JonasKaad/ProgrammingOfRobots/models/3DPrints/attachments/6_axle.stl

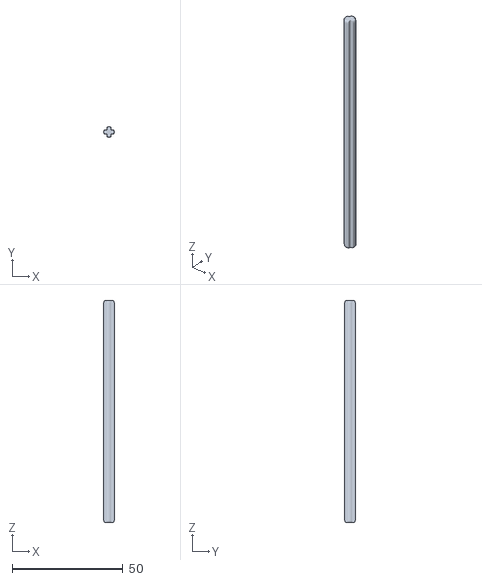
[picture p33: CAD file, 2024-05-22]
models/3DPrints/attachments/6_axle.stl
4.75 x 4.75 x 100.2
