JonasKaad/ProgrammingOfRobots/models/3DPrints/garage_bar/LBar_long.stl

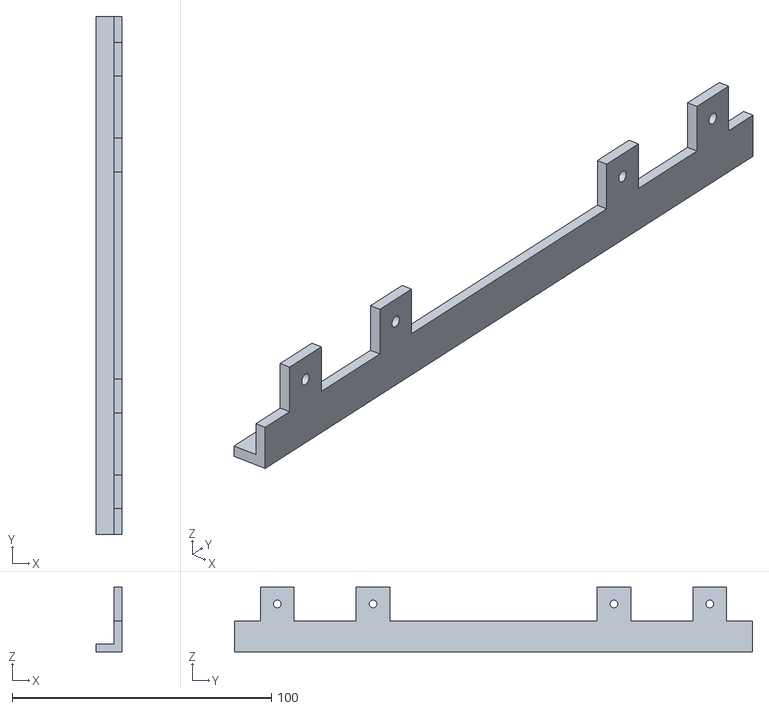
[picture p34: CAD file, 2024-05-22]
models/3DPrints/garage_bar/LBar_long.stl
10.0 x 200.0 x 25.0
