JonasKaad/ProgrammingOfRobots/models/3DPrints/gears/wormdrive_gear.stl

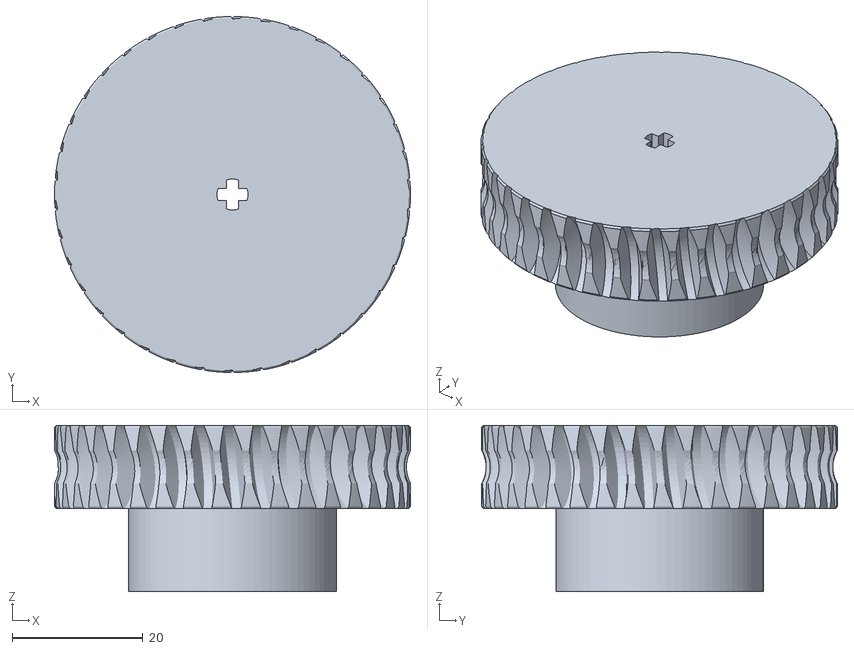
[picture p35: CAD file, 2024-05-22]
models/3DPrints/gears/wormdrive_gear.stl
54.4 x 54.4 x 25.4
