JonasKaad/ProgrammingOfRobots/models/3DPrints/supports/left_worm_drive_support.stl

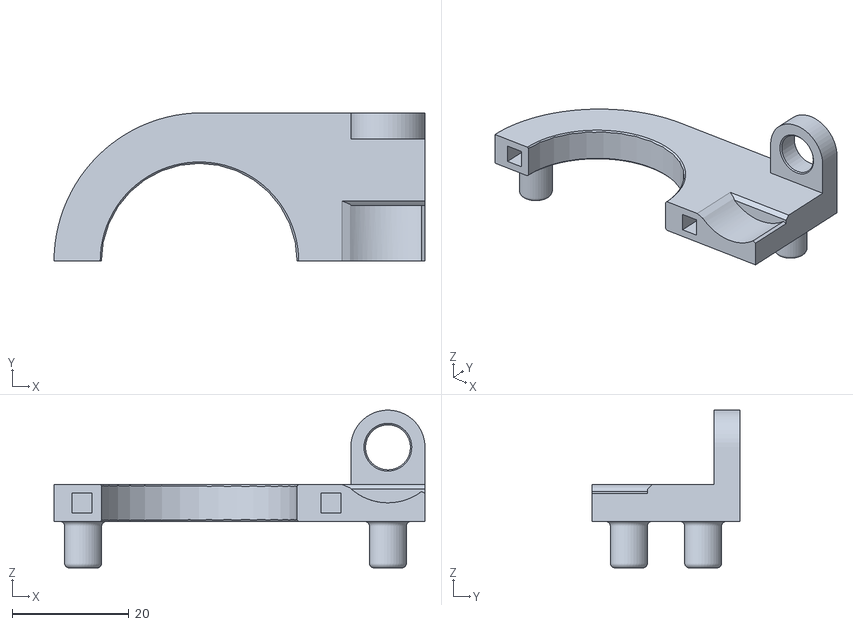
[picture p36: CAD file, 2024-05-22]
models/3DPrints/supports/left_worm_drive_support.stl
63.5 x 25.4 x 27.0
