JonasKaad/ProgrammingOfRobots/Unity/GarageTwin/Assets/Gears/WormDrive/worm_bar_gear.obj

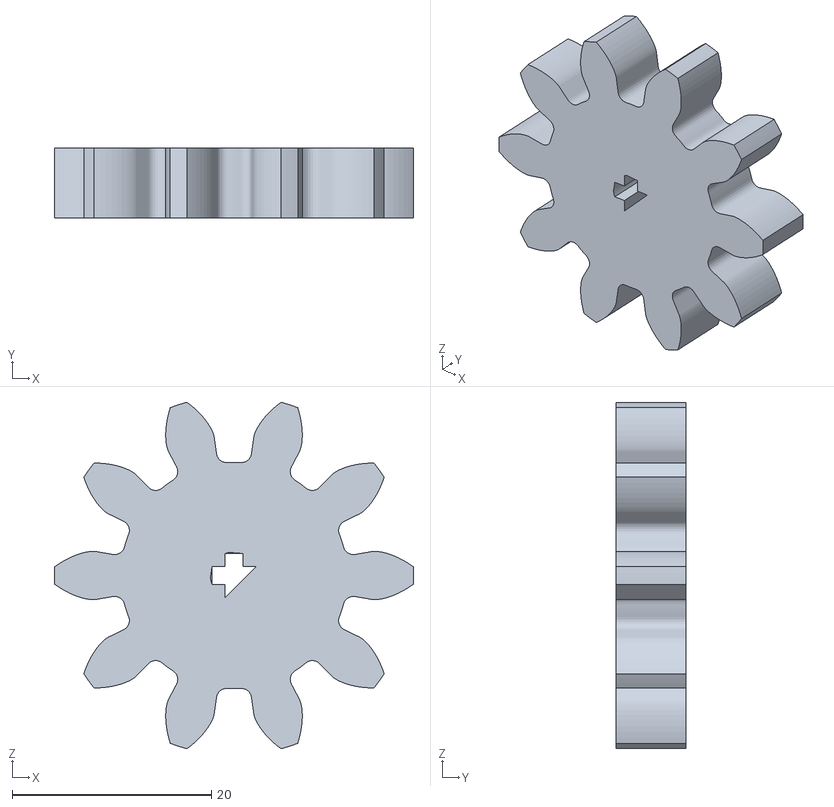
[picture p37: CAD file, 2024-05-13]
Unity/GarageTwin/Assets/Gears/WormDrive/worm_bar_gear.obj
36.0 x 7.00 x 34.7
