JonasKaad/ProgrammingOfRobots/models/3DPrints/attachments/door_connection_to_pinion.stl

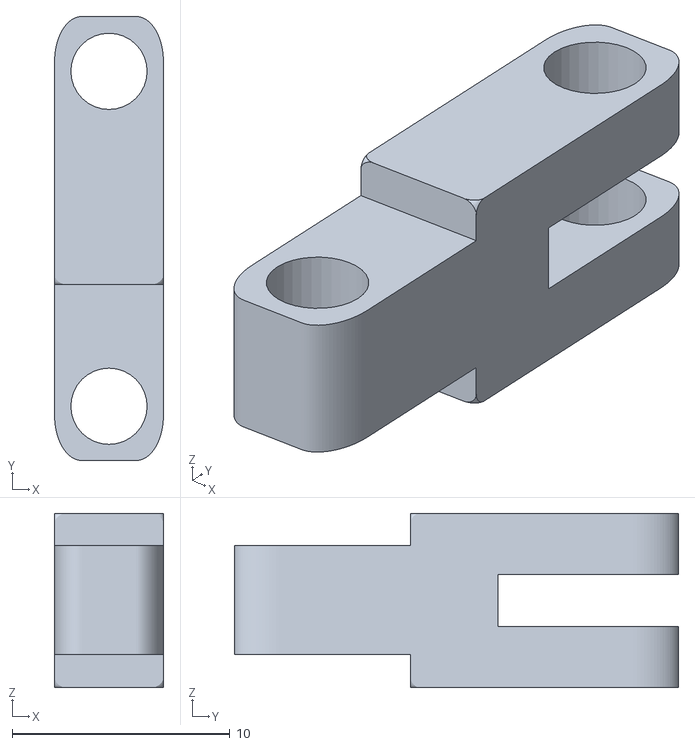
[picture p38: CAD file, 2024-05-22]
models/3DPrints/attachments/door_connection_to_pinion.stl
5.00 x 20.4 x 8.00
