JonasKaad/ProgrammingOfRobots/models/3DPrints/gears/pinion_gear.stl

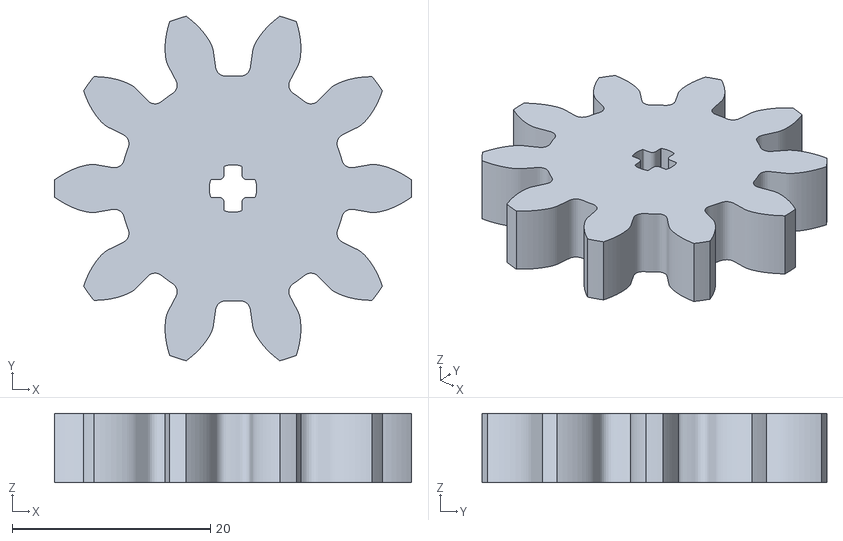
[picture p39: CAD file, 2024-05-22]
models/3DPrints/gears/pinion_gear.stl
36.0 x 34.7 x 7.00
