JonasKaad/ProgrammingOfRobots/models/3DPrints/supports/right_worm_drive_support.stl

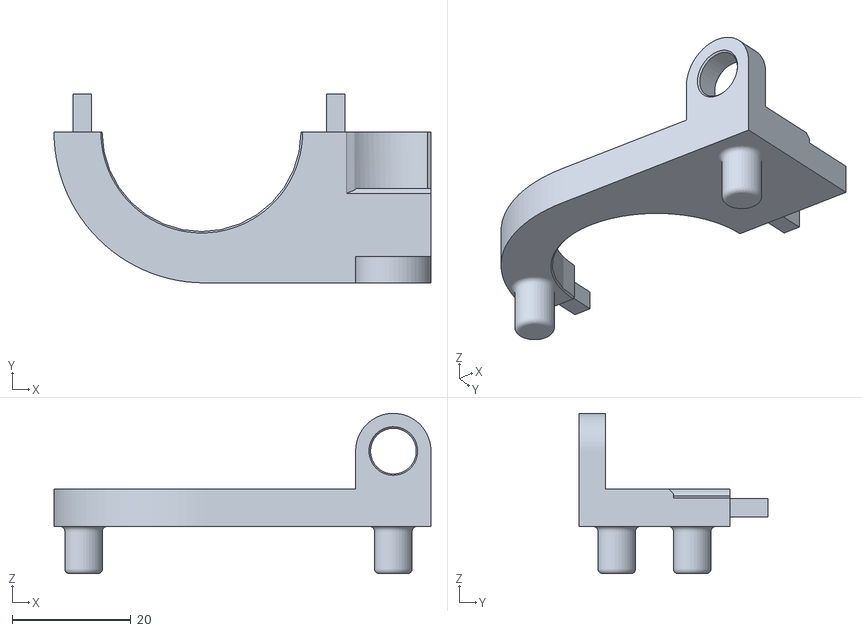
[picture p40: CAD file, 2024-05-22]
models/3DPrints/supports/right_worm_drive_support.stl
63.5 x 31.8 x 27.0
