JonasKaad/ProgrammingOfRobots/Unity/GarageTwin/Assets/Gears/WormDrive/lego_axle.obj

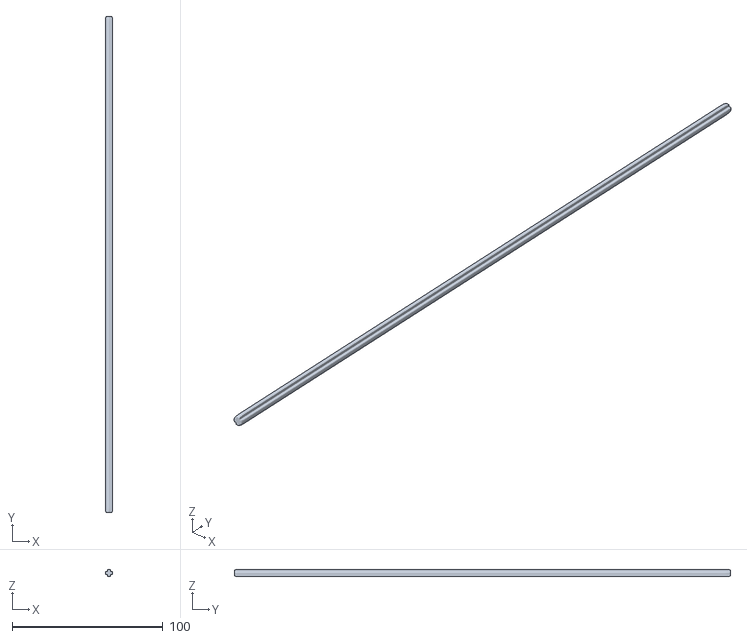
[picture p41: CAD file, 2024-05-13]
Unity/GarageTwin/Assets/Gears/WormDrive/lego_axle.obj
4.75 x 328.6 x 4.75
