JonasKaad/ProgrammingOfRobots/models/3DPrints/attachments/internal_stick_for_pinion.stl

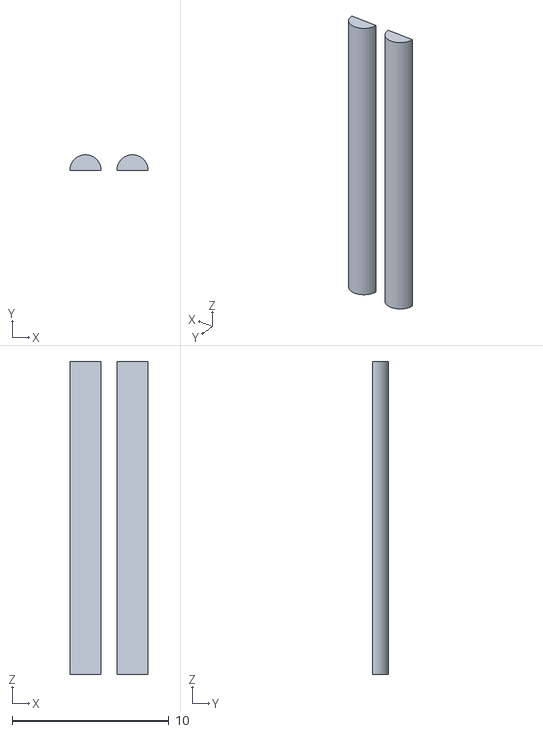
[picture p42: CAD file, 2024-05-22]
models/3DPrints/attachments/internal_stick_for_pinion.stl
5.00 x 1.00 x 20.0
