JonasKaad/ProgrammingOfRobots/models/3DPrints/gears/drive_gear_on_top_of_wormdrive.stl

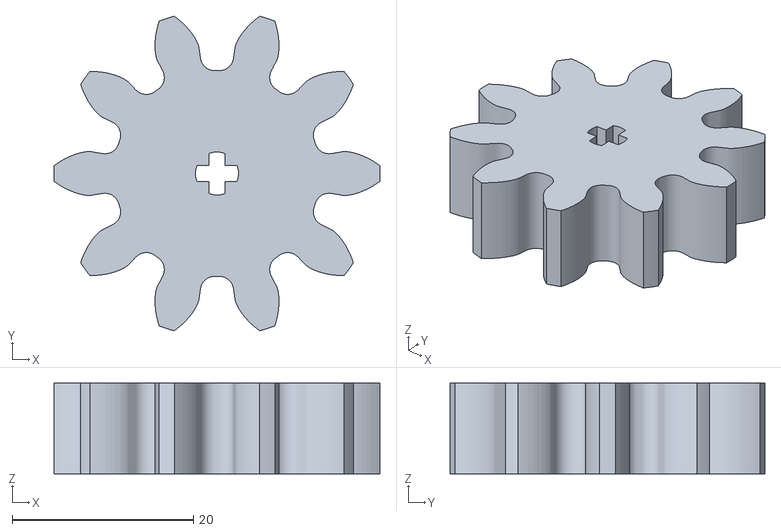
[picture p43: CAD file, 2024-05-22]
models/3DPrints/gears/drive_gear_on_top_of_wormdrive.stl
36.0 x 34.7 x 10.0
